0mnitron/Zavrsni_rad/09_vrijeme/v1.1.ino

#include "RTClib.h"

RTC_DS3231 rtc;

void setup () {
  Serial.begin(9600);
  while (!Serial) continue;
  
  if (! rtc.begin()) {
    Serial.println("Couldn't find RTC");
    while (1);
  }

  // lostPower() function reads the DS3231’s internal I2C registers to check if the chip has lost track 
  // of time. If the function returns true, we can then set the date & time.
  if (rtc.lostPower()) {
    Serial.println("RTC lost power, let's set the time!");
    // When time needs to be set on a new device, or after a power loss, the
    // following line sets the RTC to the date & time this sketch was compiled
    rtc.adjust(DateTime(F(__DATE__), F(__TIME__)));
  }
}

void loop () {
    DateTime now = rtc.now();

    Serial.print(now.year(), DEC);
    Serial.print('/');
    Serial.print(now.month(), DEC);
    Serial.print('/');
    Serial.print(now.day(), DEC);
    Serial.print("  ");
    Serial.print(now.hour(), DEC);
    Serial.print(':');
    Serial.print(now.minute(), DEC);
    Serial.print(':');
    Serial.print(now.second(), DEC);
    Serial.println();

    Serial.println();
    delay(60000);
}
