0mnitron/Zavrsni_rad/02_atmosfera/01_bme280.ino

// BME 280 - I2C communication protocol
// A5 - SCL
// A4 - SDA
// Vcc - 3.3V
// GND - GND

#include <Wire.h>
#include <Adafruit_Sensor.h>
#include <Adafruit_BME280.h>

#define SEALEVELPRESSURE_HPA (1013.25)

Adafruit_BME280 bme;

void setup() {
  Serial.begin(9600);

  if (!bme.begin(0x76)) {
    Serial.println("Could not find a valid BME280 sensor, check wiring!");
    while (1);
  }
}

void loop() {
  Serial.print("Temperature = ");
  Serial.print(bme.readTemperature());
  Serial.println("*C");

  Serial.print("Pressure = ");
  Serial.print(bme.readPressure() / 100.0F);
  Serial.println("hPa");

  Serial.print("Approx. Altitude = ");
  Serial.print(bme.readAltitude(SEALEVELPRESSURE_HPA));
  Serial.println("m");

  Serial.print("Humidity = ");
  Serial.print(bme.readHumidity());
  Serial.println("%");

  Serial.println();
  delay(1000);
}
