0mnitron/Zavrsni_rad/00-Beginning/01_BME280_initiation.ino

// BME 280 - SPI communication protocol
// Vcc = 3.3V
// GND = GND
// SCL (SCK) = 13
// SDA (SDI) = 11
// SCB (CS) = 10
// SD0 = 12

#include <Adafruit_Sensor.h>
#include <Adafruit_BME280.h>

#define BME_SCK 13
#define BME_MISO 12
#define BME_MOSI 11
#define BME_CS 10

#define SEALEVELPRESSURE_HPA (1013.25)

Adafruit_BME280 bme(BME_CS); // hardware SPI
//Adafruit_BME280 bme(BME_CS, BME_MOSI, BME_MISO, BME_SCK); // software SPI


void setup() {
    Serial.begin(9600);
    delay(200);
    Serial.println(F("BME280 test"));
    
    bme.begin();  
    
    Serial.println();
}


void loop() { 
    printValues();
    delay(2000);
}


void printValues() {
    Serial.print("Temperature = ");
    Serial.print(bme.readTemperature());
    Serial.println(" *C");

    Serial.print("Pressure = ");
    Serial.print(bme.readPressure() / 100.0F);
    Serial.println(" hPa");

    Serial.print("Approx. Altitude = ");
    Serial.print(bme.readAltitude(SEALEVELPRESSURE_HPA));
    Serial.println(" m");

    Serial.print("Humidity = ");
    Serial.print(bme.readHumidity());
    Serial.println(" %");

    Serial.println();
}
